McOrts/garage-cerberus/images/garage-cerberus_device_on.JPG

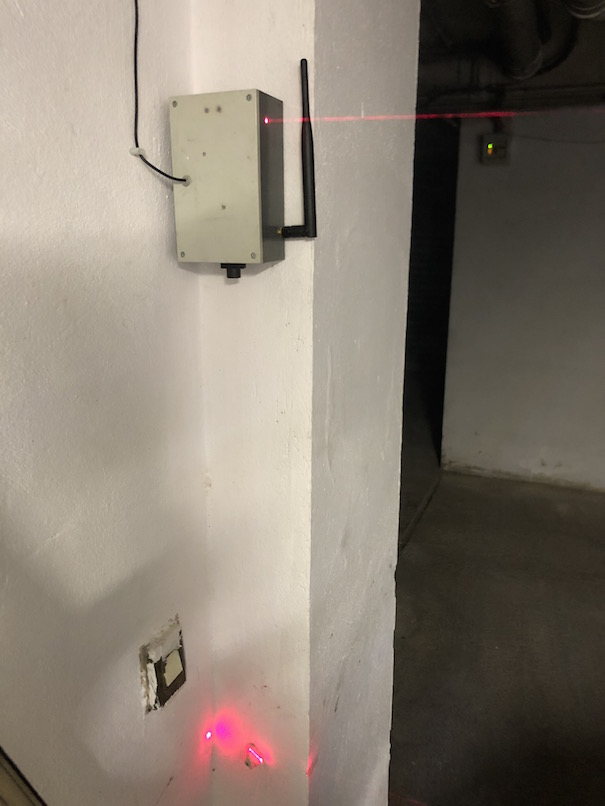
images/garage-cerberus_device_on.JPG
