McOrts/garage-cerberus/images/Raspberry Pi 3B+.png

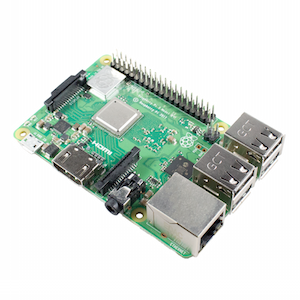
images/Raspberry Pi 3B+.png
